karoljanic/CC13_Robot/CC13_MOBILE_APP/screeny_aplikacji/aplikacja_screen2.PNG

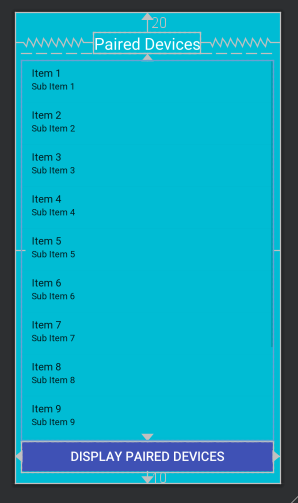
CC13_MOBILE_APP/screeny_aplikacji/aplikacja_screen2.PNG
