karoljanic/CC13_Robot/CC13_MOBILE_APP/screeny_aplikacji/aplikacja_screen3.PNG

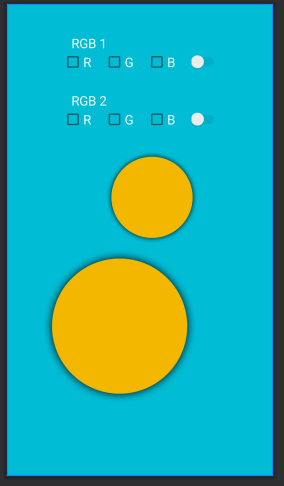
CC13_MOBILE_APP/screeny_aplikacji/aplikacja_screen3.PNG
