karoljanic/CC13_Robot/CC13_ELECTRONIC_SOFTWARE/STM32/CC13/Core/Src/main.c

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

/* Includes ------------------------------------------------------------------*/
#include "main.h"
#include "adc.h"
#include "dma.h"
#include "i2c.h"
#include "tim.h"
#include "usart.h"
#include "gpio.h"


void SystemClock_Config(void);
/* USER CODE BEGIN PFP */
extern void extern_setup(void);
extern void extern_loop(void);
extern void extern_UART_Callback(UART_HandleTypeDef *huart);
/* USER CODE END PFP */

/**
  * @brief  The application entry point.
  * @retval int
  */
int main(void)
{
  /* MCU Configuration--------------------------------------------------------*/

  /* Reset of all peripherals, Initializes the Flash interface and the Systick. */
  HAL_Init();

  /* Configure the system clock */
  SystemClock_Config();

  /* Initialize all configured peripherals */
  MX_GPIO_Init();
  MX_DMA_Init();
  MX_TIM1_Init();
  MX_I2C1_Init();
  MX_TIM3_Init();
  MX_TIM4_Init();
  MX_TIM2_Init();
  MX_USART2_UART_Init();
  MX_USART3_UART_Init();
  MX_ADC1_Init();
  /* USER CODE BEGIN 2 */

  extern_setup();

  /* USER CODE END 2 */

  /* Infinite loop */
  /* USER CODE BEGIN WHILE */
  //HAL_GPIO_WritePin(GPIOC, GPIO_PIN_13, RESET);

  while (1)
  {
    /* USER CODE END WHILE */

    /* USER CODE BEGIN 3 */
	  	extern_loop();
  }
  /* USER CODE END 3 */
}

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
/* USER CODE BEGIN 4 */

void HAL_UART_RxCpltCallback(UART_HandleTypeDef *huart)
{
	extern_UART_Callback(huart);
}

/* USER CODE END 4 */
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
