karoljanic/CC13_Robot/CC13_ELECTRONIC_SOFTWARE/STM32/CC13/Core/Inc/MPU6050.h

#ifndef _MPU6050_H_
#define _MPU6050_H_

#include "I2Cdev.h"
#include "MATH_STRUCTURES.h"
#include "FIXED.h"


#define MPU6050_ADDRESS_AD0_LOW     0xD0 // address pin low (GND), default for InvenSense evaluation board
#define MPU6050_ADDRESS_AD0_HIGH    0xD1 // address pin high (VCC)
#define MPU6050_DEFAULT_ADDRESS     MPU6050_ADDRESS_AD0_LOW

#define MPU6050_RA_XG_OFFS_TC       0x00 //[7] PWR_MODE, [6:1] XG_OFFS_TC, [0] OTP_BNK_VLD
#define MPU6050_RA_YG_OFFS_TC       0x01 //[7] PWR_MODE, [6:1] YG_OFFS_TC, [0] OTP_BNK_VLD
#define MPU6050_RA_ZG_OFFS_TC       0x02 //[7] PWR_MODE, [6:1] ZG_OFFS_TC, [0] OTP_BNK_VLD
#define MPU6050_RA_X_FINE_GAIN      0x03 //[7:0] X_FINE_GAIN
#define MPU6050_RA_Y_FINE_GAIN      0x04 //[7:0] Y_FINE_GAIN
#define MPU6050_RA_Z_FINE_GAIN      0x05 //[7:0] Z_FINE_GAIN
#define MPU6050_RA_XA_OFFS_H        0x06 //[15:0] XA_OFFS
#define MPU6050_RA_XA_OFFS_L_TC     0x07
#define MPU6050_RA_YA_OFFS_H        0x08 //[15:0] YA_OFFS
#define MPU6050_RA_YA_OFFS_L_TC     0x09
#define MPU6050_RA_ZA_OFFS_H        0x0A //[15:0] ZA_OFFS
#define MPU6050_RA_ZA_OFFS_L_TC     0x0B
#define MPU6050_RA_SELF_TEST_X      0x0D //[7:5] XA_TEST[4-2], [4:0] XG_TEST[4-0]
#define MPU6050_RA_SELF_TEST_Y      0x0E //[7:5] YA_TEST[4-2], [4:0] YG_TEST[4-0]
#define MPU6050_RA_SELF_TEST_Z      0x0F //[7:5] ZA_TEST[4-2], [4:0] ZG_TEST[4-0]
#define MPU6050_RA_SELF_TEST_A      0x10 //[5:4] XA_TEST[1-0], [3:2] YA_TEST[1-0], [1:0] ZA_TEST[1-0]
#define MPU6050_RA_XG_OFFS_USRH     0x13 //[15:0] XG_OFFS_USR
#define MPU6050_RA_XG_OFFS_USRL     0x14
#define MPU6050_RA_YG_OFFS_USRH     0x15 //[15:0] YG_OFFS_USR
#define MPU6050_RA_YG_OFFS_USRL     0x16
#define MPU6050_RA_ZG_OFFS_USRH     0x17 //[15:0] ZG_OFFS_USR
#define MPU6050_RA_ZG_OFFS_USRL     0x18
#define MPU6050_RA_SMPLRT_DIV       0x19
#define MPU6050_RA_CONFIG           0x1A
#define MPU6050_RA_GYRO_CONFIG      0x1B
#define MPU6050_RA_ACCEL_CONFIG     0x1C
#define MPU6050_RA_FF_THR           0x1D
#define MPU6050_RA_FF_DUR           0x1E
#define MPU6050_RA_MOT_THR          0x1F
#define MPU6050_RA_MOT_DUR          0x20
#define MPU6050_RA_ZRMOT_THR        0x21
#define MPU6050_RA_ZRMOT_DUR        0x22
#define MPU6050_RA_FIFO_EN          0x23
#define MPU6050_RA_I2C_MST_CTRL     0x24
#define MPU6050_RA_I2C_SLV0_ADDR    0x25
#define MPU6050_RA_I2C_SLV0_REG     0x26
#define MPU6050_RA_I2C_SLV0_CTRL    0x27
#define MPU6050_RA_I2C_SLV1_ADDR    0x28
#define MPU6050_RA_I2C_SLV1_REG     0x29
#define MPU6050_RA_I2C_SLV1_CTRL    0x2A
#define MPU6050_RA_I2C_SLV2_ADDR    0x2B
#define MPU6050_RA_I2C_SLV2_REG     0x2C
#define MPU6050_RA_I2C_SLV2_CTRL    0x2D
#define MPU6050_RA_I2C_SLV3_ADDR    0x2E
#define MPU6050_RA_I2C_SLV3_REG     0x2F
#define MPU6050_RA_I2C_SLV3_CTRL    0x30
#define MPU6050_RA_I2C_SLV4_ADDR    0x31
#define MPU6050_RA_I2C_SLV4_REG     0x32
#define MPU6050_RA_I2C_SLV4_DO      0x33
#define MPU6050_RA_I2C_SLV4_CTRL    0x34
#define MPU6050_RA_I2C_SLV4_DI      0x35
#define MPU6050_RA_I2C_MST_STATUS   0x36
#define MPU6050_RA_INT_PIN_CFG      0x37
#define MPU6050_RA_INT_ENABLE       0x38
#define MPU6050_RA_DMP_INT_STATUS   0x39
#define MPU6050_RA_INT_STATUS       0x3A
#define MPU6050_RA_ACCEL_XOUT_H     0x3B
#define MPU6050_RA_ACCEL_XOUT_L     0x3C
#define MPU6050_RA_ACCEL_YOUT_H     0x3D
#define MPU6050_RA_ACCEL_YOUT_L     0x3E
#define MPU6050_RA_ACCEL_ZOUT_H     0x3F
#define MPU6050_RA_ACCEL_ZOUT_L     0x40
#define MPU6050_RA_TEMP_OUT_H       0x41
#define MPU6050_RA_TEMP_OUT_L       0x42
#define MPU6050_RA_GYRO_XOUT_H      0x43
#define MPU6050_RA_GYRO_XOUT_L      0x44
#define MPU6050_RA_GYRO_YOUT_H      0x45
#define MPU6050_RA_GYRO_YOUT_L      0x46
#define MPU6050_RA_GYRO_ZOUT_H      0x47
#define MPU6050_RA_GYRO_ZOUT_L      0x48
#define MPU6050_RA_EXT_SENS_DATA_00 0x49
#define MPU6050_RA_EXT_SENS_DATA_01 0x4A
#define MPU6050_RA_EXT_SENS_DATA_02 0x4B
#define MPU6050_RA_EXT_SENS_DATA_03 0x4C
#define MPU6050_RA_EXT_SENS_DATA_04 0x4D
#define MPU6050_RA_EXT_SENS_DATA_05 0x4E
#define MPU6050_RA_EXT_SENS_DATA_06 0x4F
#define MPU6050_RA_EXT_SENS_DATA_07 0x50
#define MPU6050_RA_EXT_SENS_DATA_08 0x51
#define MPU6050_RA_EXT_SENS_DATA_09 0x52
#define MPU6050_RA_EXT_SENS_DATA_10 0x53
#define MPU6050_RA_EXT_SENS_DATA_11 0x54
#define MPU6050_RA_EXT_SENS_DATA_12 0x55
#define MPU6050_RA_EXT_SENS_DATA_13 0x56
#define MPU6050_RA_EXT_SENS_DATA_14 0x57
#define MPU6050_RA_EXT_SENS_DATA_15 0x58
#define MPU6050_RA_EXT_SENS_DATA_16 0x59
#define MPU6050_RA_EXT_SENS_DATA_17 0x5A
#define MPU6050_RA_EXT_SENS_DATA_18 0x5B
#define MPU6050_RA_EXT_SENS_DATA_19 0x5C
#define MPU6050_RA_EXT_SENS_DATA_20 0x5D
#define MPU6050_RA_EXT_SENS_DATA_21 0x5E
#define MPU6050_RA_EXT_SENS_DATA_22 0x5F
#define MPU6050_RA_EXT_SENS_DATA_23 0x60
#define MPU6050_RA_MOT_DETECT_STATUS    0x61
#define MPU6050_RA_I2C_SLV0_DO      0x63
#define MPU6050_RA_I2C_SLV1_DO      0x64
#define MPU6050_RA_I2C_SLV2_DO      0x65
#define MPU6050_RA_I2C_SLV3_DO      0x66
#define MPU6050_RA_I2C_MST_DELAY_CTRL   0x67
#define MPU6050_RA_SIGNAL_PATH_RESET    0x68
#define MPU6050_RA_MOT_DETECT_CTRL      0x69
#define MPU6050_RA_USER_CTRL        0x6A
#define MPU6050_RA_PWR_MGMT_1       0x6B
#define MPU6050_RA_PWR_MGMT_2       0x6C
#define MPU6050_RA_BANK_SEL         0x6D
#define MPU6050_RA_MEM_START_ADDR   0x6E
#define MPU6050_RA_MEM_R_W          0x6F
#define MPU6050_RA_DMP_CFG_1        0x70
#define MPU6050_RA_DMP_CFG_2        0x71
#define MPU6050_RA_FIFO_COUNTH      0x72
#define MPU6050_RA_FIFO_COUNTL      0x73
#define MPU6050_RA_FIFO_R_W         0x74
#define MPU6050_RA_WHO_AM_I         0x75

#define MPU6050_SELF_TEST_XA_1_BIT     0x07
#define MPU6050_SELF_TEST_XA_1_LENGTH  0x03
#define MPU6050_SELF_TEST_XA_2_BIT     0x05
#define MPU6050_SELF_TEST_XA_2_LENGTH  0x02
#define MPU6050_SELF_TEST_YA_1_BIT     0x07
#define MPU6050_SELF_TEST_YA_1_LENGTH  0x03
#define MPU6050_SELF_TEST_YA_2_BIT     0x03
#define MPU6050_SELF_TEST_YA_2_LENGTH  0x02
#define MPU6050_SELF_TEST_ZA_1_BIT     0x07
#define MPU6050_SELF_TEST_ZA_1_LENGTH  0x03
#define MPU6050_SELF_TEST_ZA_2_BIT     0x01
#define MPU6050_SELF_TEST_ZA_2_LENGTH  0x02

#define MPU6050_SELF_TEST_XG_1_BIT     0x04
#define MPU6050_SELF_TEST_XG_1_LENGTH  0x05
#define MPU6050_SELF_TEST_YG_1_BIT     0x04
#define MPU6050_SELF_TEST_YG_1_LENGTH  0x05
#define MPU6050_SELF_TEST_ZG_1_BIT     0x04
#define MPU6050_SELF_TEST_ZG_1_LENGTH  0x05

#define MPU6050_TC_PWR_MODE_BIT     7
#define MPU6050_TC_OFFSET_BIT       6
#define MPU6050_TC_OFFSET_LENGTH    6
#define MPU6050_TC_OTP_BNK_VLD_BIT  0

#define MPU6050_VDDIO_LEVEL_VLOGIC  0
#define MPU6050_VDDIO_LEVEL_VDD     1

#define MPU6050_CFG_EXT_SYNC_SET_BIT    5
#define MPU6050_CFG_EXT_SYNC_SET_LENGTH 3
#define MPU6050_CFG_DLPF_CFG_BIT    2
#define MPU6050_CFG_DLPF_CFG_LENGTH 3

#define MPU6050_EXT_SYNC_DISABLED       0x0
#define MPU6050_EXT_SYNC_TEMP_OUT_L     0x1
#define MPU6050_EXT_SYNC_GYRO_XOUT_L    0x2
#define MPU6050_EXT_SYNC_GYRO_YOUT_L    0x3
#define MPU6050_EXT_SYNC_GYRO_ZOUT_L    0x4
#define MPU6050_EXT_SYNC_ACCEL_XOUT_L   0x5
#define MPU6050_EXT_SYNC_ACCEL_YOUT_L   0x6
#define MPU6050_EXT_SYNC_ACCEL_ZOUT_L   0x7

#define MPU6050_DLPF_BW_256         0x00
#define MPU6050_DLPF_BW_188         0x01
#define MPU6050_DLPF_BW_98          0x02
#define MPU6050_DLPF_BW_42          0x03
#define MPU6050_DLPF_BW_20          0x04
#define MPU6050_DLPF_BW_10          0x05
#define MPU6050_DLPF_BW_5           0x06

#define MPU6050_GCONFIG_FS_SEL_BIT      4
#define MPU6050_GCONFIG_FS_SEL_LENGTH   2

#define MPU6050_GYRO_FS_250         0x00
#define MPU6050_GYRO_FS_500         0x01
#define MPU6050_GYRO_FS_1000        0x02
#define MPU6050_GYRO_FS_2000        0x03

#define MPU6050_ACONFIG_XA_ST_BIT           7
#define MPU6050_ACONFIG_YA_ST_BIT           6
#define MPU6050_ACONFIG_ZA_ST_BIT           5
#define MPU6050_ACONFIG_AFS_SEL_BIT         4
#define MPU6050_ACONFIG_AFS_SEL_LENGTH      2
#define MPU6050_ACONFIG_ACCEL_HPF_BIT       2
#define MPU6050_ACONFIG_ACCEL_HPF_LENGTH    3

#define MPU6050_ACCEL_FS_2          0x00
#define MPU6050_ACCEL_FS_4          0x01
#define MPU6050_ACCEL_FS_8          0x02
#define MPU6050_ACCEL_FS_16         0x03

#define MPU6050_DHPF_RESET          0x00
#define MPU6050_DHPF_5              0x01
#define MPU6050_DHPF_2P5            0x02
#define MPU6050_DHPF_1P25           0x03
#define MPU6050_DHPF_0P63           0x04
#define MPU6050_DHPF_HOLD           0x07

#define MPU6050_TEMP_FIFO_EN_BIT    7
#define MPU6050_XG_FIFO_EN_BIT      6
#define MPU6050_YG_FIFO_EN_BIT      5
#define MPU6050_ZG_FIFO_EN_BIT      4
#define MPU6050_ACCEL_FIFO_EN_BIT   3
#define MPU6050_SLV2_FIFO_EN_BIT    2
#define MPU6050_SLV1_FIFO_EN_BIT    1
#define MPU6050_SLV0_FIFO_EN_BIT    0

#define MPU6050_MULT_MST_EN_BIT     7
#define MPU6050_WAIT_FOR_ES_BIT     6
#define MPU6050_SLV_3_FIFO_EN_BIT   5
#define MPU6050_I2C_MST_P_NSR_BIT   4
#define MPU6050_I2C_MST_CLK_BIT     3
#define MPU6050_I2C_MST_CLK_LENGTH  4

#define MPU6050_CLOCK_DIV_348       0x0
#define MPU6050_CLOCK_DIV_333       0x1
#define MPU6050_CLOCK_DIV_320       0x2
#define MPU6050_CLOCK_DIV_308       0x3
#define MPU6050_CLOCK_DIV_296       0x4
#define MPU6050_CLOCK_DIV_286       0x5
#define MPU6050_CLOCK_DIV_276       0x6
#define MPU6050_CLOCK_DIV_267       0x7
#define MPU6050_CLOCK_DIV_258       0x8
#define MPU6050_CLOCK_DIV_500       0x9
#define MPU6050_CLOCK_DIV_471       0xA
#define MPU6050_CLOCK_DIV_444       0xB
#define MPU6050_CLOCK_DIV_421       0xC
#define MPU6050_CLOCK_DIV_400       0xD
#define MPU6050_CLOCK_DIV_381       0xE
#define MPU6050_CLOCK_DIV_364       0xF

#define MPU6050_I2C_SLV_RW_BIT      7
#define MPU6050_I2C_SLV_ADDR_BIT    6
#define MPU6050_I2C_SLV_ADDR_LENGTH 7
#define MPU6050_I2C_SLV_EN_BIT      7
#define MPU6050_I2C_SLV_BYTE_SW_BIT 6
#define MPU6050_I2C_SLV_REG_DIS_BIT 5
#define MPU6050_I2C_SLV_GRP_BIT     4
#define MPU6050_I2C_SLV_LEN_BIT     3
#define MPU6050_I2C_SLV_LEN_LENGTH  4

#define MPU6050_I2C_SLV4_RW_BIT         7
#define MPU6050_I2C_SLV4_ADDR_BIT       6
#define MPU6050_I2C_SLV4_ADDR_LENGTH    7
#define MPU6050_I2C_SLV4_EN_BIT         7
#define MPU6050_I2C_SLV4_INT_EN_BIT     6
#define MPU6050_I2C_SLV4_REG_DIS_BIT    5
#define MPU6050_I2C_SLV4_MST_DLY_BIT    4
#define MPU6050_I2C_SLV4_MST_DLY_LENGTH 5

#define MPU6050_MST_PASS_THROUGH_BIT    7
#define MPU6050_MST_I2C_SLV4_DONE_BIT   6
#define MPU6050_MST_I2C_LOST_ARB_BIT    5
#define MPU6050_MST_I2C_SLV4_NACK_BIT   4
#define MPU6050_MST_I2C_SLV3_NACK_BIT   3
#define MPU6050_MST_I2C_SLV2_NACK_BIT   2
#define MPU6050_MST_I2C_SLV1_NACK_BIT   1
#define MPU6050_MST_I2C_SLV0_NACK_BIT   0

#define MPU6050_INTCFG_INT_LEVEL_BIT        7
#define MPU6050_INTCFG_INT_OPEN_BIT         6
#define MPU6050_INTCFG_LATCH_INT_EN_BIT     5
#define MPU6050_INTCFG_INT_RD_CLEAR_BIT     4
#define MPU6050_INTCFG_FSYNC_INT_LEVEL_BIT  3
#define MPU6050_INTCFG_FSYNC_INT_EN_BIT     2
#define MPU6050_INTCFG_I2C_BYPASS_EN_BIT    1
#define MPU6050_INTCFG_CLKOUT_EN_BIT        0

#define MPU6050_INTMODE_ACTIVEHIGH  0x00
#define MPU6050_INTMODE_ACTIVELOW   0x01

#define MPU6050_INTDRV_PUSHPULL     0x00
#define MPU6050_INTDRV_OPENDRAIN    0x01

#define MPU6050_INTLATCH_50USPULSE  0x00
#define MPU6050_INTLATCH_WAITCLEAR  0x01

#define MPU6050_INTCLEAR_STATUSREAD 0x00
#define MPU6050_INTCLEAR_ANYREAD    0x01

#define MPU6050_INTERRUPT_FF_BIT            7
#define MPU6050_INTERRUPT_MOT_BIT           6
#define MPU6050_INTERRUPT_ZMOT_BIT          5
#define MPU6050_INTERRUPT_FIFO_OFLOW_BIT    4
#define MPU6050_INTERRUPT_I2C_MST_INT_BIT   3
#define MPU6050_INTERRUPT_PLL_RDY_INT_BIT   2
#define MPU6050_INTERRUPT_DMP_INT_BIT       1
#define MPU6050_INTERRUPT_DATA_RDY_BIT      0

#define MPU6050_DMPINT_5_BIT            5
#define MPU6050_DMPINT_4_BIT            4
#define MPU6050_DMPINT_3_BIT            3
#define MPU6050_DMPINT_2_BIT            2
#define MPU6050_DMPINT_1_BIT            1
#define MPU6050_DMPINT_0_BIT            0

#define MPU6050_MOTION_MOT_XNEG_BIT     7
#define MPU6050_MOTION_MOT_XPOS_BIT     6
#define MPU6050_MOTION_MOT_YNEG_BIT     5
#define MPU6050_MOTION_MOT_YPOS_BIT     4
#define MPU6050_MOTION_MOT_ZNEG_BIT     3
#define MPU6050_MOTION_MOT_ZPOS_BIT     2
#define MPU6050_MOTION_MOT_ZRMOT_BIT    0

#define MPU6050_DELAYCTRL_DELAY_ES_SHADOW_BIT   7
#define MPU6050_DELAYCTRL_I2C_SLV4_DLY_EN_BIT   4
#define MPU6050_DELAYCTRL_I2C_SLV3_DLY_EN_BIT   3
#define MPU6050_DELAYCTRL_I2C_SLV2_DLY_EN_BIT   2
#define MPU6050_DELAYCTRL_I2C_SLV1_DLY_EN_BIT   1
#define MPU6050_DELAYCTRL_I2C_SLV0_DLY_EN_BIT   0

#define MPU6050_PATHRESET_GYRO_RESET_BIT    2
#define MPU6050_PATHRESET_ACCEL_RESET_BIT   1
#define MPU6050_PATHRESET_TEMP_RESET_BIT    0

#define MPU6050_DETECT_ACCEL_ON_DELAY_BIT       5
#define MPU6050_DETECT_ACCEL_ON_DELAY_LENGTH    2
#define MPU6050_DETECT_FF_COUNT_BIT             3
#define MPU6050_DETECT_FF_COUNT_LENGTH          2
#define MPU6050_DETECT_MOT_COUNT_BIT            1
#define MPU6050_DETECT_MOT_COUNT_LENGTH         2

#define MPU6050_DETECT_DECREMENT_RESET  0x0
#define MPU6050_DETECT_DECREMENT_1      0x1
#define MPU6050_DETECT_DECREMENT_2      0x2
#define MPU6050_DETECT_DECREMENT_4      0x3

#define MPU6050_USERCTRL_DMP_EN_BIT             7
#define MPU6050_USERCTRL_FIFO_EN_BIT            6
#define MPU6050_USERCTRL_I2C_MST_EN_BIT         5
#define MPU6050_USERCTRL_I2C_IF_DIS_BIT         4
#define MPU6050_USERCTRL_DMP_RESET_BIT          3
#define MPU6050_USERCTRL_FIFO_RESET_BIT         2
#define MPU6050_USERCTRL_I2C_MST_RESET_BIT      1
#define MPU6050_USERCTRL_SIG_COND_RESET_BIT     0

#define MPU6050_PWR1_DEVICE_RESET_BIT   7
#define MPU6050_PWR1_SLEEP_BIT          6
#define MPU6050_PWR1_CYCLE_BIT          5
#define MPU6050_PWR1_TEMP_DIS_BIT       3
#define MPU6050_PWR1_CLKSEL_BIT         2
#define MPU6050_PWR1_CLKSEL_LENGTH      3

#define MPU6050_CLOCK_INTERNAL          0x00
#define MPU6050_CLOCK_PLL_XGYRO         0x01
#define MPU6050_CLOCK_PLL_YGYRO         0x02
#define MPU6050_CLOCK_PLL_ZGYRO         0x03
#define MPU6050_CLOCK_PLL_EXT32K        0x04
#define MPU6050_CLOCK_PLL_EXT19M        0x05
#define MPU6050_CLOCK_KEEP_RESET        0x07

#define MPU6050_PWR2_LP_WAKE_CTRL_BIT       7
#define MPU6050_PWR2_LP_WAKE_CTRL_LENGTH    2
#define MPU6050_PWR2_STBY_XA_BIT            5
#define MPU6050_PWR2_STBY_YA_BIT            4
#define MPU6050_PWR2_STBY_ZA_BIT            3
#define MPU6050_PWR2_STBY_XG_BIT            2
#define MPU6050_PWR2_STBY_YG_BIT            1
#define MPU6050_PWR2_STBY_ZG_BIT            0

#define MPU6050_WAKE_FREQ_1P25      0x0
#define MPU6050_WAKE_FREQ_2P5       0x1
#define MPU6050_WAKE_FREQ_5         0x2
#define MPU6050_WAKE_FREQ_10        0x3

#define MPU6050_BANKSEL_PRFTCH_EN_BIT       6
#define MPU6050_BANKSEL_CFG_USER_BANK_BIT   5
#define MPU6050_BANKSEL_MEM_SEL_BIT         4
#define MPU6050_BANKSEL_MEM_SEL_LENGTH      5

#define MPU6050_WHO_AM_I_BIT        6
#define MPU6050_WHO_AM_I_LENGTH     6

#define MPU6050_DMP_MEMORY_BANKS        8
#define MPU6050_DMP_MEMORY_BANK_SIZE    256
#define MPU6050_DMP_MEMORY_CHUNK_SIZE   16

#define pgm_read_byte(addr) (*(const unsigned char *)(addr))

#define MPU6050_DMP_CODE_SIZE       1929    // dmpMemory[]
#define MPU6050_DMP_CONFIG_SIZE     192     // dmpConfig[]
#define MPU6050_DMP_UPDATES_SIZE    47      // dmpUpdates[]

/* ================================================================================================ *
 | DMP 42-byte FIFO packet structure:                                           |
 |                                                                                                  |
 | [QUAT W][      ][QUAT X][      ][QUAT Y][      ][QUAT Z][      ][GYRO X][      ][GYRO Y][      ] |
 |   0   1   2   3   4   5   6   7   8   9  10  11  12  13  14  15  16  17  18  19  20  21  22  23  |
 |                                                                                                  |
 | [GYRO Z][      ][ACC X ][      ][ACC Y ][      ][ACC Z ][      ][      ]                         |
 |  24  25  26  27  28  29  30  31  32  33  34  35  36  37  38  39  40  41                          |
 * ================================================================================================ */

// this block of memory gets written to the MPU on start-up, and it seems
// to be volatile memory, so it has to be done each time (it only takes ~1
// second though)


const unsigned char dmpMemory[MPU6050_DMP_CODE_SIZE] = {
    // bank 0, 256 bytes
    0xFB, 0x00, 0x00, 0x3E, 0x00, 0x0B, 0x00, 0x36, 0x00, 0x01, 0x00, 0x02, 0x00, 0x03, 0x00, 0x00,
    0x00, 0x65, 0x00, 0x54, 0xFF, 0xEF, 0x00, 0x00, 0xFA, 0x80, 0x00, 0x0B, 0x12, 0x82, 0x00, 0x01,
    0x00, 0x02, 0x00, 0x00, 0x00, 0x00, 0x00, 0x00, 0x00, 0x00, 0x00, 0x00, 0x00, 0x00, 0x00, 0x00,
    0x00, 0x28, 0x00, 0x00, 0xFF, 0xFF, 0x45, 0x81, 0xFF, 0xFF, 0xFA, 0x72, 0x00, 0x00, 0x00, 0x00,
    0x00, 0x00, 0x03, 0xE8, 0x00, 0x00, 0x00, 0x01, 0x00, 0x01, 0x7F, 0xFF, 0xFF, 0xFE, 0x80, 0x01,
    0x00, 0x1B, 0x00, 0x00, 0x00, 0x00, 0x00, 0x00, 0x00, 0x00, 0x00, 0x00, 0x00, 0x00, 0x00, 0x00,
    0x00, 0x3E, 0x03, 0x30, 0x40, 0x00, 0x00, 0x00, 0x02, 0xCA, 0xE3, 0x09, 0x3E, 0x80, 0x00, 0x00,
    0x20, 0x00, 0x00, 0x00, 0x00, 0x00, 0x00, 0x00, 0x40, 0x00, 0x00, 0x00, 0x60, 0x00, 0x00, 0x00,
    0x41, 0xFF, 0x00, 0x00, 0x00, 0x00, 0x0B, 0x2A, 0x00, 0x00, 0x16, 0x55, 0x00, 0x00, 0x21, 0x82,
    0xFD, 0x87, 0x26, 0x50, 0xFD, 0x80, 0x00, 0x00, 0x00, 0x1F, 0x00, 0x00, 0x00, 0x05, 0x80, 0x00,
    0x00, 0x00, 0x00, 0x00, 0x00, 0x01, 0x00, 0x00, 0x00, 0x02, 0x00, 0x00, 0x00, 0x03, 0x00, 0x00,
    0x40, 0x00, 0x00, 0x00, 0x00, 0x00, 0x04, 0x6F, 0x00, 0x02, 0x65, 0x32, 0x00, 0x00, 0x5E, 0xC0,
    0x40, 0x00, 0x00, 0x00, 0x00, 0x00, 0x00, 0x00, 0x00, 0x00, 0x00, 0x00, 0x00, 0x00, 0x00, 0x00,
    0xFB, 0x8C, 0x6F, 0x5D, 0xFD, 0x5D, 0x08, 0xD9, 0x00, 0x7C, 0x73, 0x3B, 0x00, 0x6C, 0x12, 0xCC,
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
    0xA3, 0xB2, 0xA3, 0xA3, 0xA3, 0xA3, 0xA3, 0xA3, 0xB0, 0x87, 0xB5, 0x99, 0xF1, 0xA3, 0xA3, 0xA3,
    0x98, 0xF1, 0xA3, 0xA3, 0xA3, 0xA3, 0x97, 0xA3, 0xA3, 0xA3, 0xA3, 0xF3, 0x9B, 0xA3, 0xA3, 0xDC,
    0xB9, 0xA7, 0xF1, 0x26, 0x26, 0x26, 0xD8, 0xD8, 0xFF
};

const unsigned char dmpConfig[MPU6050_DMP_CONFIG_SIZE] = {
//  BANK    OFFSET  LENGTH  [DATA]
    0x03,   0x7B,   0x03,   0x4C, 0xCD, 0x6C,         // FCFG_1 inv_set_gyro_calibration
    0x03,   0xAB,   0x03,   0x36, 0x56, 0x76,         // FCFG_3 inv_set_gyro_calibration
    0x00,   0x68,   0x04,   0x02, 0xCB, 0x47, 0xA2,   // D_0_104 inv_set_gyro_calibration
    0x02,   0x18,   0x04,   0x00, 0x05, 0x8B, 0xC1,   // D_0_24 inv_set_gyro_calibration
    0x01,   0x0C,   0x04,   0x00, 0x00, 0x00, 0x00,   // D_1_152 inv_set_accel_calibration
    0x03,   0x7F,   0x06,   0x0C, 0xC9, 0x2C, 0x97, 0x97, 0x97, // FCFG_2 inv_set_accel_calibration
    0x03,   0x89,   0x03,   0x26, 0x46, 0x66,         // FCFG_7 inv_set_accel_calibration
    0x00,   0x6C,   0x02,   0x20, 0x00,               // D_0_108 inv_set_accel_calibration
    0x02,   0x40,   0x04,   0x00, 0x00, 0x00, 0x00,   // CPASS_MTX_00 inv_set_compass_calibration
    0x02,   0x44,   0x04,   0x00, 0x00, 0x00, 0x00,   // CPASS_MTX_01
    0x02,   0x48,   0x04,   0x00, 0x00, 0x00, 0x00,   // CPASS_MTX_02
    0x02,   0x4C,   0x04,   0x00, 0x00, 0x00, 0x00,   // CPASS_MTX_10
    0x02,   0x50,   0x04,   0x00, 0x00, 0x00, 0x00,   // CPASS_MTX_11
    0x02,   0x54,   0x04,   0x00, 0x00, 0x00, 0x00,   // CPASS_MTX_12
    0x02,   0x58,   0x04,   0x00, 0x00, 0x00, 0x00,   // CPASS_MTX_20
    0x02,   0x5C,   0x04,   0x00, 0x00, 0x00, 0x00,   // CPASS_MTX_21
    0x02,   0xBC,   0x04,   0x00, 0x00, 0x00, 0x00,   // CPASS_MTX_22
    0x01,   0xEC,   0x04,   0x00, 0x00, 0x40, 0x00,   // D_1_236 inv_apply_endian_accel
    0x03,   0x7F,   0x06,   0x0C, 0xC9, 0x2C, 0x97, 0x97, 0x97, // FCFG_2 inv_set_mpu_sensors
    0x04,   0x02,   0x03,   0x0D, 0x35, 0x5D,         // CFG_MOTION_BIAS inv_turn_on_bias_from_no_motion
    0x04,   0x09,   0x04,   0x87, 0x2D, 0x35, 0x3D,   // FCFG_5 inv_set_bias_update
    0x00,   0xA3,   0x01,   0x00,                     // D_0_163 inv_set_dead_zone
                 // SPECIAL 0x01 = enable interrupts
    0x00,   0x00,   0x00,   0x01, // SET INT_ENABLE at i=22, SPECIAL INSTRUCTION
    0x07,   0x86,   0x01,   0xFE,                     // CFG_6 inv_set_fifo_interupt
    0x07,   0x41,   0x05,   0xF1, 0x20, 0x28, 0x30, 0x38, // CFG_8 inv_send_quaternion
    0x07,   0x7E,   0x01,   0x30,                     // CFG_16 inv_set_footer
    0x07,   0x46,   0x01,   0x9A,                     // CFG_GYRO_SOURCE inv_send_gyro
    0x07,   0x47,   0x04,   0xF1, 0x28, 0x30, 0x38,   // CFG_9 inv_send_gyro -> inv_construct3_fifo
    0x07,   0x6C,   0x04,   0xF1, 0x28, 0x30, 0x38,   // CFG_12 inv_send_accel -> inv_construct3_fifo
    0x02,   0x16,   0x02,   0x00, 0x01                // D_0_22 inv_set_fifo_rate

    // This very last 0x01 WAS a 0x09, which drops the FIFO rate down to 20 Hz. 0x07 is 25 Hz,
    // 0x01 is 100Hz. Going faster than 100Hz (0x00=200Hz) tends to result in very noisy data.
    // DMP output frequency is calculated easily using this equation: (200Hz / (1 + value))

    // It is important to make sure the host processor can keep up with reading and processing
    // the FIFO output at the desired rate. Handling FIFO overflow cleanly is also a good idea.
};

const unsigned char dmpUpdates[MPU6050_DMP_UPDATES_SIZE] = {
    0x01,   0xB2,   0x02,   0xFF, 0xFF,
    0x01,   0x90,   0x04,   0x09, 0x23, 0xA1, 0x35,
    0x01,   0x6A,   0x02,   0x06, 0x00,
    0x01,   0x60,   0x08,   0x00, 0x00, 0x00, 0x00, 0x00, 0x00, 0x00, 0x00,
    0x00,   0x60,   0x04,   0x40, 0x00, 0x00, 0x00,
    0x01,   0x62,   0x02,   0x00, 0x00,
    0x00,   0x60,   0x04,   0x00, 0x40, 0x00, 0x00
};

class MPU6050 {
    public:
        MPU6050();
        MPU6050(uint8_t address);

        void initialize();
        bool testConnection();

        // SMPLRT_DIV register
        uint8_t getRate();
        void setRate(uint8_t rate);

        // CONFIG register
        void setExternalFrameSync(uint8_t sync);
        void setDLPFMode(uint8_t bandwidth);

        /*GYRO_CONFIG register
        	0x00 --> +/- 250 degrees/s
        	0x01 --> +/- 500 degrees/s
        	0x02 --> +/- 1000 degrees/s
        	0x03 --> +/- 2000 degres/s
        */void setFullScaleGyroscopeRange(uint8_t range);
		
        /* ACCEL_CONFIG register
     		0x00 --> +/- 2g
			0x01 --> +/- 4g
			0x02 --> +/- 8g
			0x03 --> +/- 16g
        */void setFullScaleAccelerationRange(uint8_t range);

        void setDHPFMode(uint8_t mode);

        // FF_THR register
        void setFreefallDetectionThreshold(uint8_t threshold);

        // FF_DUR register
        void setFreefallDetectionDuration(uint8_t duration);

        // MOT_THR register
        void setMotionDetectionThreshold(uint8_t threshold);

        // MOT_DUR register
        void setMotionDetectionDuration(uint8_t duration);

        // ZRMOT_THR register
        void setZeroMotionDetectionThreshold(uint8_t threshold);

        // ZRMOT_DUR register
        void setZeroMotionDetectionDuration(uint8_t duration);

        // I2C_SLAVE
        void setSlaveAddress(uint8_t num, uint8_t address);

        // INT_STATUS REGISTER
        uint8_t getIntStatus();
        void setIntEnabled(uint8_t enabled);

        // ACCEL_*OUT_* registers
        void getAcceleration(Vector<int16_t>* v);
        void getAccelerationFloat(Vector<float>* v);
        int16_t getAccelerationX();
        int16_t getAccelerationY();
        int16_t getAccelerationZ();

        // TEMP_OUT_* registers
        int16_t getTemperature();

        // GYRO_*OUT_* registers
        void getRotation(Vector<int16_t>* v);
        void getRotationFloat(Vector<float>* v);
        int16_t getRotationX();
        int16_t getRotationY();
        int16_t getRotationZ();

        // MOT_DETECT_STATUS register
        bool getZeroMotionDetected();

        void reset();
        void resetFIFO();
        void resetI2CMaster();
        void resetSensors();

        void setSleepEnabled(bool enabled);
        void setFIFOEnabled(bool enabled);
        void setI2CMasterModeEnabled(bool enabled);
        void setClockSource(uint8_t source);
        void setOTPBankValid(bool enabled);

        // FIFO_COUNT_* registers
        uint16_t getFIFOCount();

        // FIFO_R_W register
        uint8_t getFIFOByte();
        void setFIFOByte(uint8_t data);
        void getFIFOBytes(uint8_t *data, uint8_t length);

        // WHO_AM_I register
        uint8_t getDeviceID();
        void setDeviceID(uint8_t id);

        // XA_OFFS_* registers
        void setXAccelerationOffset(int16_t offset);

        // YA_OFFS_* register
        void setYAccelerationOffset(int16_t offset);

        // ZA_OFFS_* register
        void setZAccelerationOffset(int16_t offset);

        // XG_OFFS_USR* registers
        void setXGyroscopeOffset(int16_t offset);

        // YG_OFFS_USR* register
        void setYGyroscopeOffset(int16_t offset);

        // ZG_OFFS_USR* register
        void setZGyroscopeOffset(int16_t offset);

        // DMP_INT_STATUS
        bool getIntDMPStatus();
        void setDMPEnabled(bool enabled);
        void resetDMP();

        // BANK_SEL register
        void setMemoryBank(uint8_t bank, bool prefetchEnabled=false, bool userBank=false);
        
        // MEM_START_ADDR register
        void setMemoryStartAddress(uint8_t address);
        
        // MEM_R_W register
        uint8_t readMemoryByte();
        void writeMemoryByte(uint8_t data);
        void readMemoryBlock(uint8_t *data, uint16_t dataSize, uint8_t bank=0, uint8_t address=0);
        bool writeMemoryBlock(const uint8_t *data, uint16_t dataSize, uint8_t bank=0, uint8_t address=0, bool verify=true);
        bool writeProgMemoryBlock(const uint8_t *data, uint16_t dataSize, uint8_t bank=0, uint8_t address=0, bool verify=true);

        bool writeDMPConfigurationSet(const uint8_t *data, uint16_t dataSize);
        bool writeProgDMPConfigurationSet(const uint8_t *data, uint16_t dataSize);

        // DMP_CFG_1 register
        uint8_t getDMPConfig1();
        void setDMPConfig1(uint8_t config);

        // DMP_CFG_2 register
        uint8_t getDMPConfig2();
        void setDMPConfig2(uint8_t config);

		uint8_t DMPInitialize();
		bool DMPPacketAvailable();

		uint8_t DMPGetAcceleration(Vector<int16_t> *v, const uint8_t* packet=0);
		uint8_t DMPGetQuaternion(int16_t *data, const uint8_t* packet=0);
		uint8_t DMPGetQuaternion(Quaternion<float> *q, const uint8_t* packet=0);
		uint8_t DMPGetRotation(Vector<int16_t> *v, const uint8_t* packet=0);
		uint8_t DMPGetLinearAcceleration(Vector<int16_t> *v, Vector<int16_t> *vRaw, Vector<float> *gravity);
		uint8_t DMPGetGravity(Vector<float> *v, Quaternion<float> *q);

		uint8_t DMPGetEuler(float *data, Quaternion<float> *q);
		uint8_t DMPGetYawPitchRoll(float *data, Quaternion<float> *q, Vector<float> *gravity);

		uint8_t DMPProcessFIFOPacket(const unsigned char *dmpData);
		uint8_t DMPReadAndProcessFIFOPacket(uint8_t numPackets, uint8_t *processed=NULL);

		uint16_t DMPGetFIFOPacketSize();

    private:
        uint8_t devAddr;
        uint8_t buffer[14];

        uint8_t accelScale;
        uint8_t gyroScale;

        uint8_t *dmpPacketBuffer;
        uint16_t dmpPacketSize;
};

#endif /* _MPU6050_H_ */
